OPEnSLab-OSU/SapFlowMeterOld/CODE/hub_v9/hub_v9.ino

// ================================================================
// ===              INCLUDE CONFIGURATION FILE                  ===
// ===    INCLUDE DECLARATIONS, STRUCTS, AND FUNCTIONS FROM     ===
// ===            OTHER FILES AS SET IN CONFIG.H                ===
// ================================================================

// Config has to be first has it hold all user specified options
#include "config.h"


// Preamble includes any relevant subroutine files based 
// on options specified in the above config
#include "loom_preamble.h"


// ================================================================ 
// ===                           SETUP                          ===
// ================================================================ 
void setup() 
{
  
	// LOOM_begin calls any relevant (based on config) LOOM device setup functions
	Loom_begin();	

	// Any custom setup code

}


// ================================================================ 
// ===                        MAIN LOOP                         ===
// ================================================================ 
void loop() 
{
	OSCBundle bndl, send_bndl; 

#if is_sapflow == 1
  run_sapflowmeter(&send_bndl);
#endif
	additional_loop_checks();

}
